MrDaila007/joltik-v2-mini-sumo/CAD/Front plate_20mm.SLDPRT

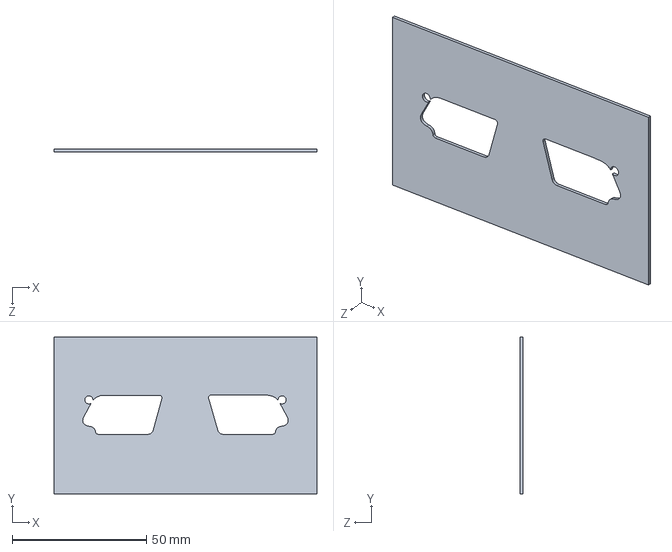
[picture p15: CAD file, 2026-03-14]
CAD/Front plate_20mm.SLDPRT
98.0 x 58.4 x 1.00 mm
