MrDaila007/joltik-v2-mini-sumo/CAD/Front plate_10mm.SLDPRT

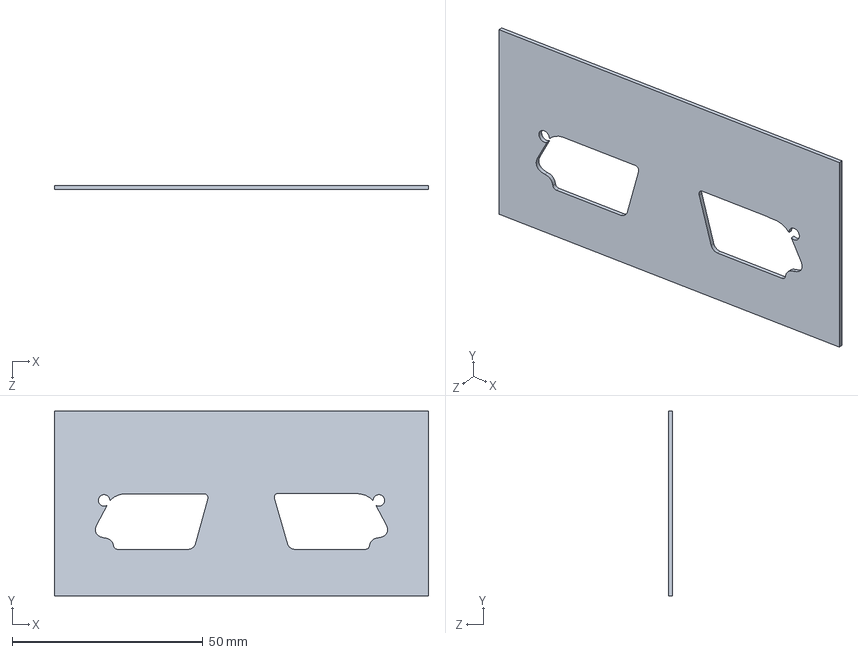
[picture p16: CAD file, 2026-03-14]
CAD/Front plate_10mm.SLDPRT
98.0 x 48.4 x 1.00 mm
