MrDaila007/joltik-v2-mini-sumo/CAD/JST - XH - Thru (V) - 4Pin - 2.54mm.SLDPRT

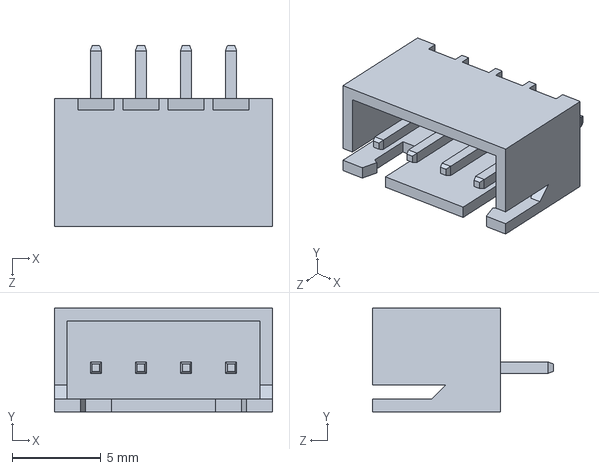
[picture p17: CAD file, 2026-03-14]
CAD/JST - XH - Thru (V) - 4Pin - 2.54mm.SLDPRT
12.3 x 5.84 x 10.2 mm
