MrDaila007/joltik-v2-mini-sumo/CAD/Charger_port.SLDPRT

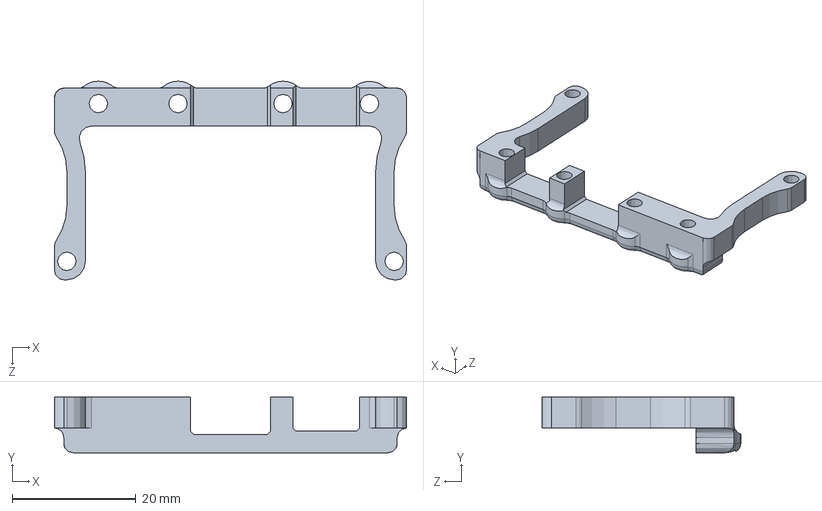
[picture p18: CAD file, 2026-03-14]
CAD/Charger_port.SLDPRT
57.0 x 9.00 x 32.2 mm
