MrDaila007/joltik-v2-mini-sumo/CAD/Servo_gear_1.SLDPRT

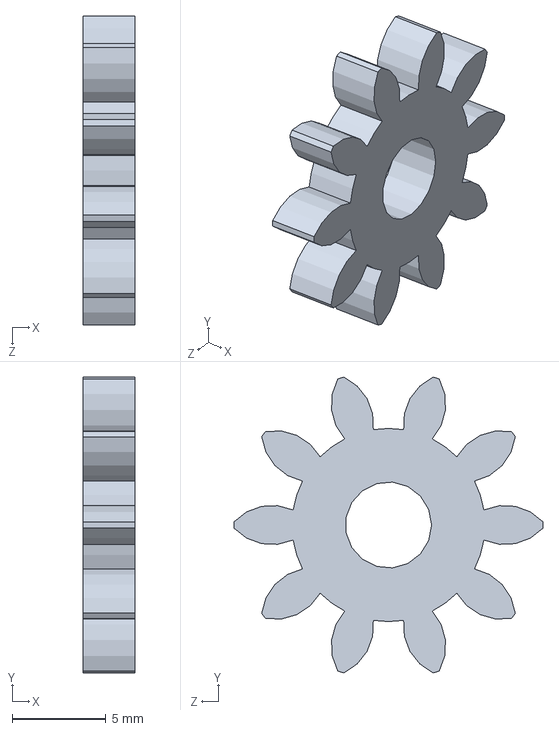
[picture p19: CAD file, 2026-03-14]
CAD/Servo_gear_1.SLDPRT
2.80 x 15.8 x 16.5 mm
