MrDaila007/joltik-v2-mini-sumo/CAD/Base plate.SLDPRT

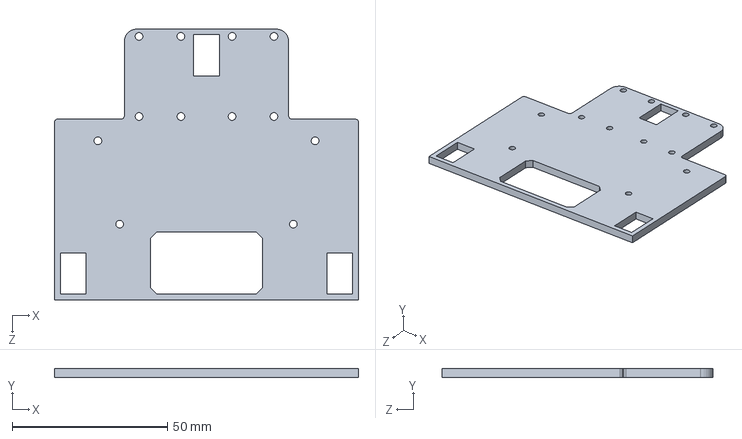
[picture p20: CAD file, 2026-03-14]
CAD/Base plate.SLDPRT
98.0 x 3.00 x 87.3 mm
