MrDaila007/joltik-v2-mini-sumo/CAD/weight boost.SLDPRT

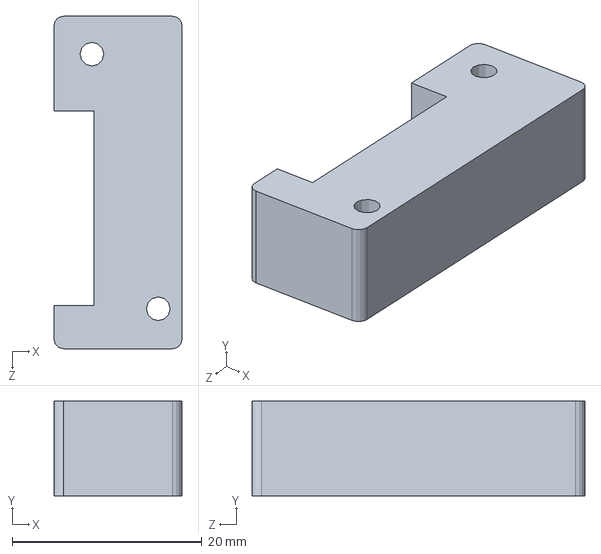
[picture p21: CAD file, 2026-03-14]
CAD/weight boost.SLDPRT
13.5 x 10.0 x 35.1 mm
