MrDaila007/joltik-v2-mini-sumo/CAD/Front plate.SLDPRT

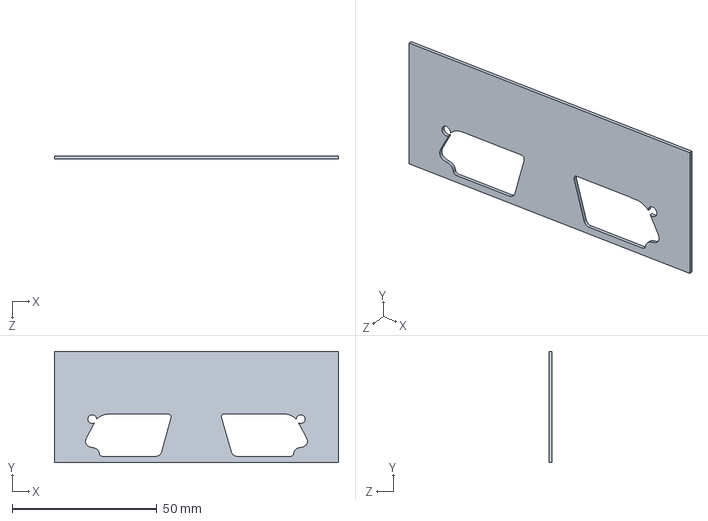
[picture p22: CAD file, 2026-03-14]
CAD/Front plate.SLDPRT
98.0 x 38.4 x 1.00 mm
