MrDaila007/joltik-v2-mini-sumo/CAD/JS7444_wheel.SLDPRT

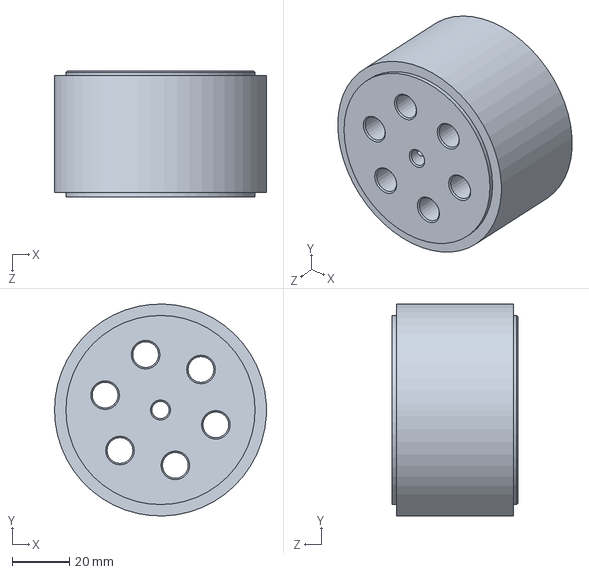
[picture p23: CAD file, 2026-03-14]
CAD/JS7444_wheel.SLDPRT
74.0 x 74.0 x 44.0 mm
