MrDaila007/joltik-v2-mini-sumo/CAD/pololu-QTR-1a.SLDPRT

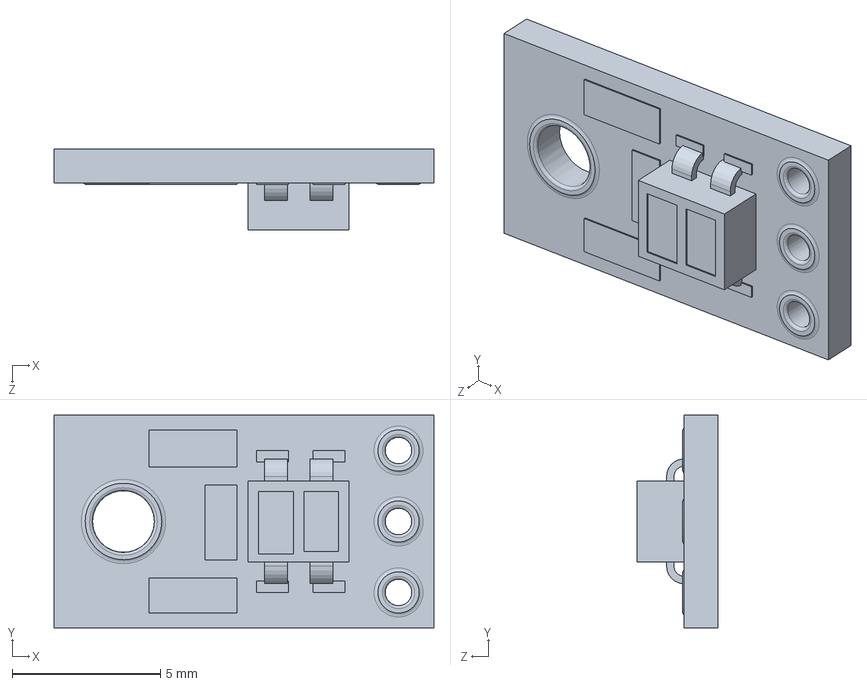
[picture p24: CAD file, 2026-03-14]
CAD/pololu-QTR-1a.SLDPRT
12.8 x 7.17 x 2.73 mm
