MrDaila007/joltik-v2-mini-sumo/CAD/Motor.SLDPRT

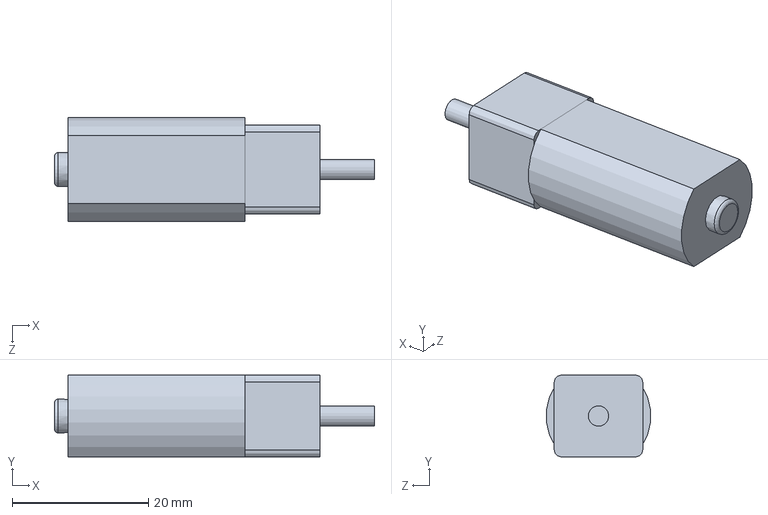
[picture p25: CAD file, 2026-03-14]
CAD/Motor.SLDPRT
47.0 x 12.0 x 15.3 mm
