MrDaila007/joltik-v2-mini-sumo/CAD/Battery.SLDPRT

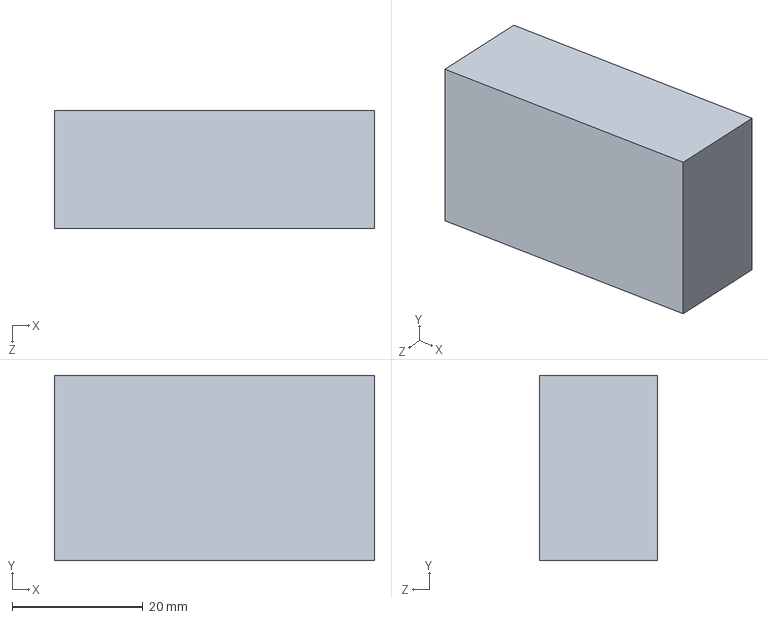
[picture p26: CAD file, 2026-03-14]
CAD/Battery.SLDPRT
49.0 x 28.4 x 18.1 mm
