MrDaila007/joltik-v2-mini-sumo/CAD/Motor bracket.SLDPRT

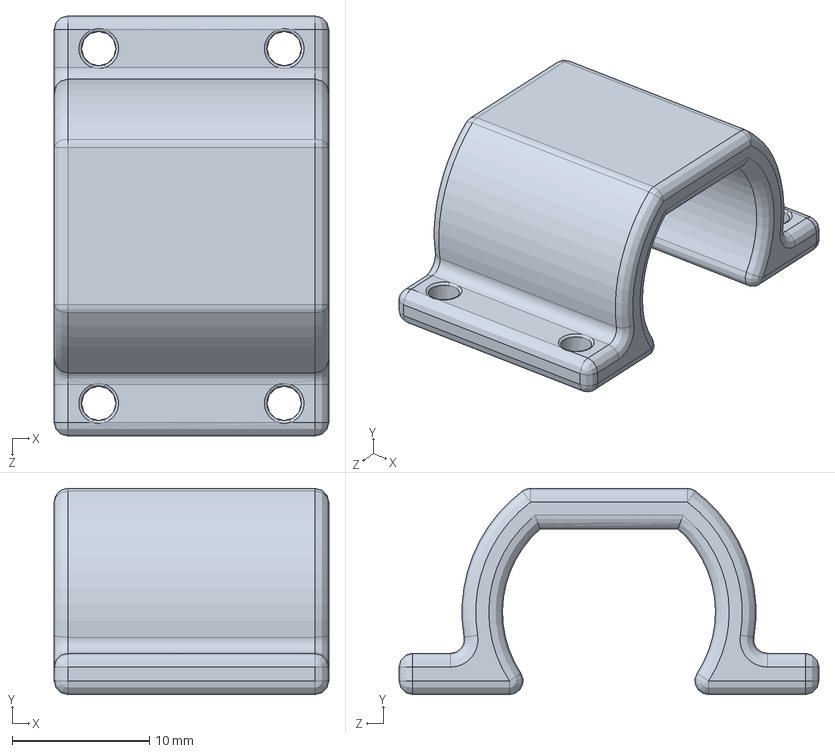
[picture p27: CAD file, 2026-03-14]
CAD/Motor bracket.SLDPRT
20.0 x 15.0 x 30.6 mm
