MrDaila007/joltik-v2-mini-sumo/CAD/Sumo_weel.SLDPRT

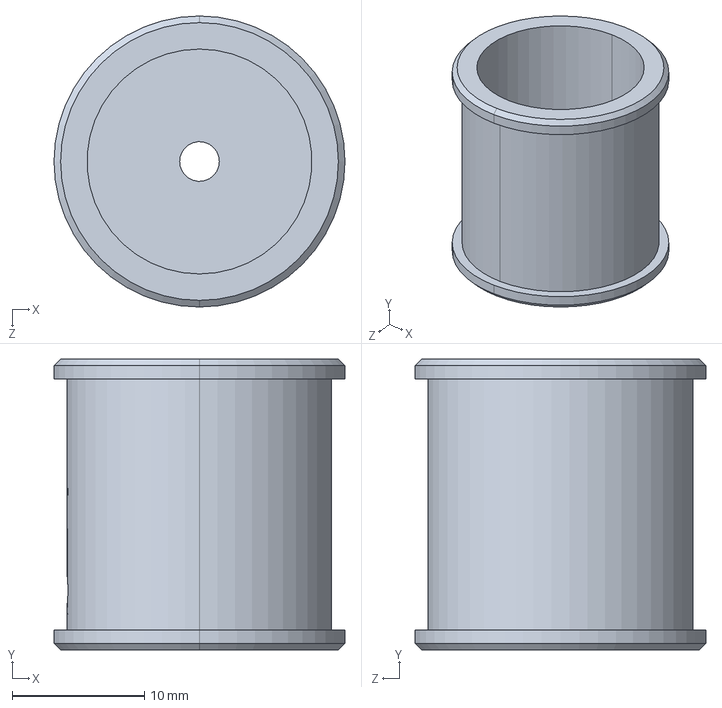
[picture p28: CAD file, 2026-03-14]
CAD/Sumo_weel.SLDPRT
22.0 x 22.0 x 22.0 mm
