MrDaila007/joltik-v2-mini-sumo/CAD/Tire_new.SLDPRT

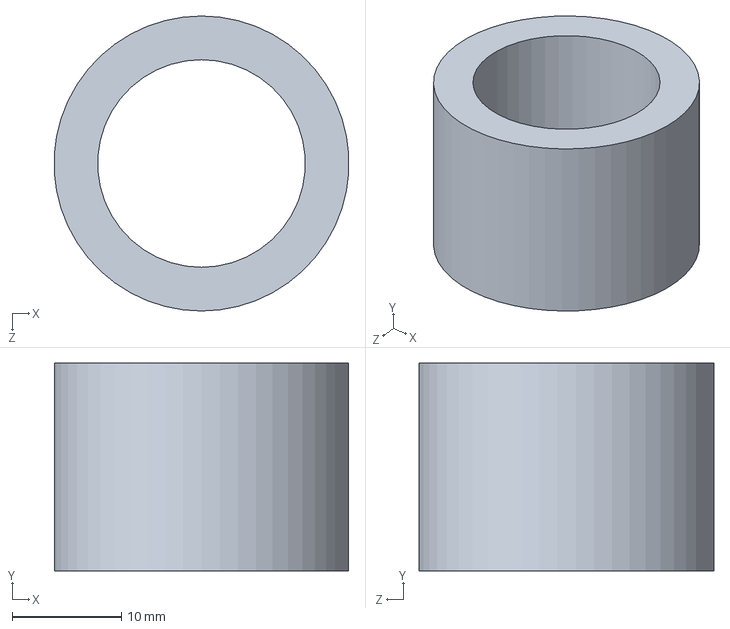
[picture p29: CAD file, 2026-03-14]
CAD/Tire_new.SLDPRT
26.9 x 19.0 x 27.0 mm
