MrDaila007/joltik-v2-mini-sumo/CAD/Servo_gear_2.SLDPRT

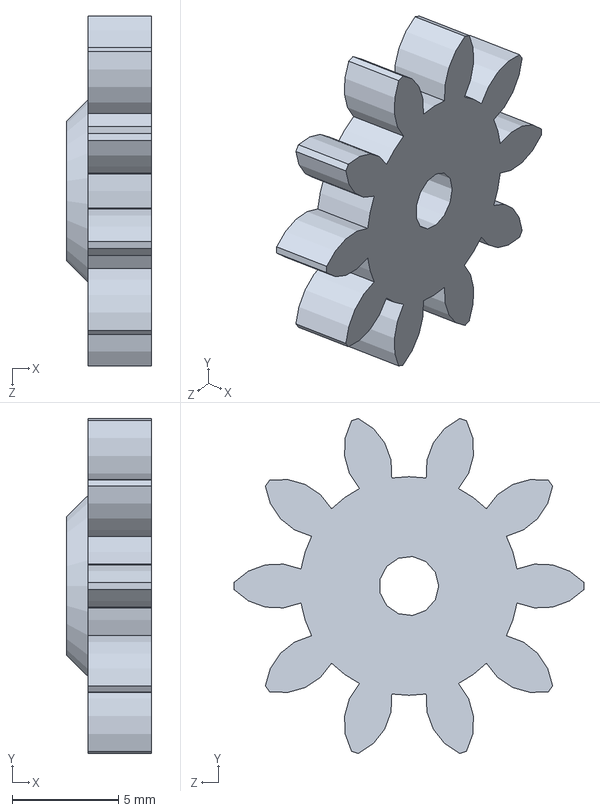
[picture p30: CAD file, 2026-03-14]
CAD/Servo_gear_2.SLDPRT
4.00 x 15.8 x 16.5 mm
