MrDaila007/joltik-v2-mini-sumo/CAD/Motor_spacer.SLDPRT

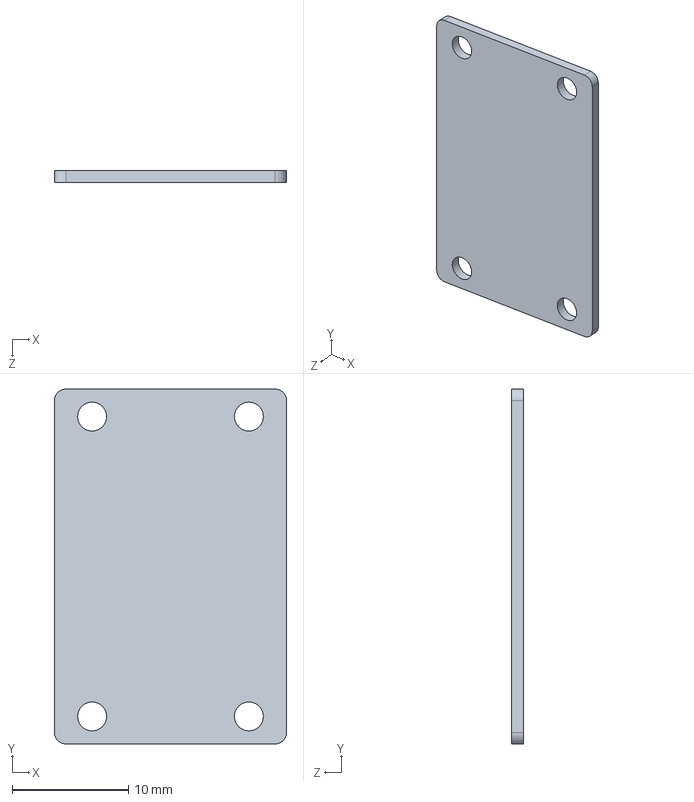
[picture p31: CAD file, 2026-03-14]
CAD/Motor_spacer.SLDPRT
20.0 x 30.6 x 1.00 mm
