MrDaila007/joltik-v2-mini-sumo/CAD/Top cover.SLDPRT

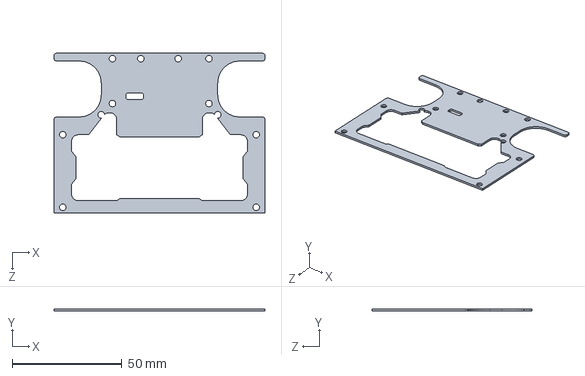
[picture p32: CAD file, 2026-03-14]
CAD/Top cover.SLDPRT
96.0 x 1.00 x 72.6 mm
