MrDaila007/joltik-v2-mini-sumo/CAD/Servo.SLDASM

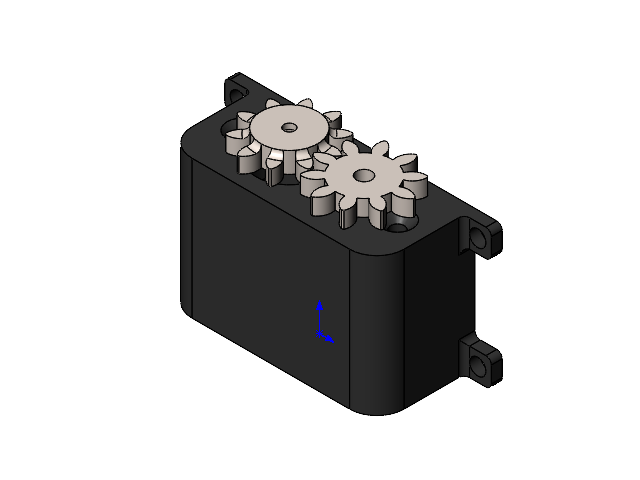
[picture p33: CAD file, 2026-03-14]
CAD/Servo.SLDASM
Servo mount
spur gear_iso x 2
