MrDaila007/joltik-v2-mini-sumo/CAD/Joltik2.0 Assembly Base+sensors.SLDASM

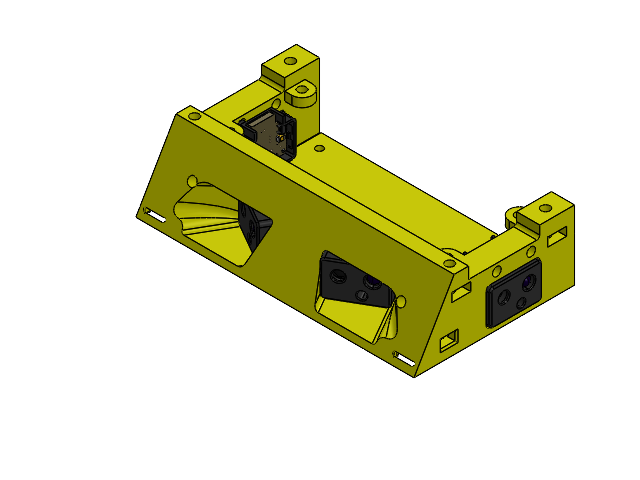
[picture p34: CAD file, 2026-03-14]
CAD/Joltik2.0 Assembly Base+sensors.SLDASM
Main_1
Board.STEP x 4
1608.STEP x 40
LED-1608.STEP x 8
LED-5MM.STEP x 4
SOT-23.STEP x 4
SOIC-08N.STEP x 4
TSSP40_Right angle bend.STEP x 4
2012.STEP x 4
SMD-RS-VR.STEP x 4
MO Casing.STEP x 4
