MrDaila007/joltik-v2-mini-sumo/CAD/MAKER-OBJECT.SLDASM

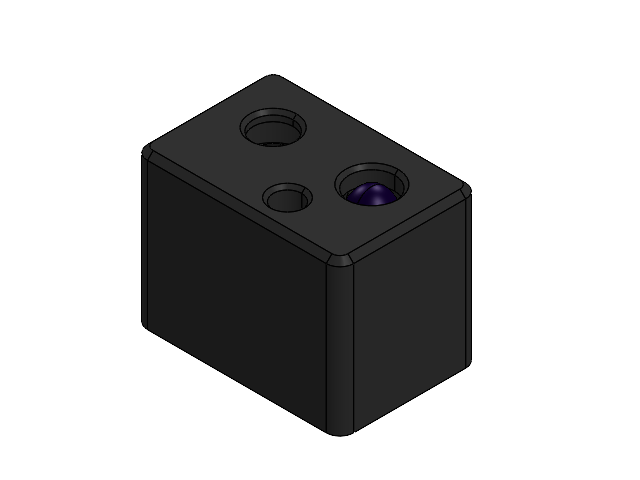
[picture p35: CAD file, 2026-03-14]
CAD/MAKER-OBJECT.SLDASM
Board.STEP
1608.STEP x 10
LED-1608.STEP x 2
LED-5MM.STEP
SOT-23.STEP
SOIC-08N.STEP
TSSP40_Right angle bend.STEP
2012.STEP
SMD-RS-VR.STEP
MO Casing.STEP
